mbarszcz-pcb/c64-rf-modulator-replacement/images/c64-rf-modulator-render-top.PNG

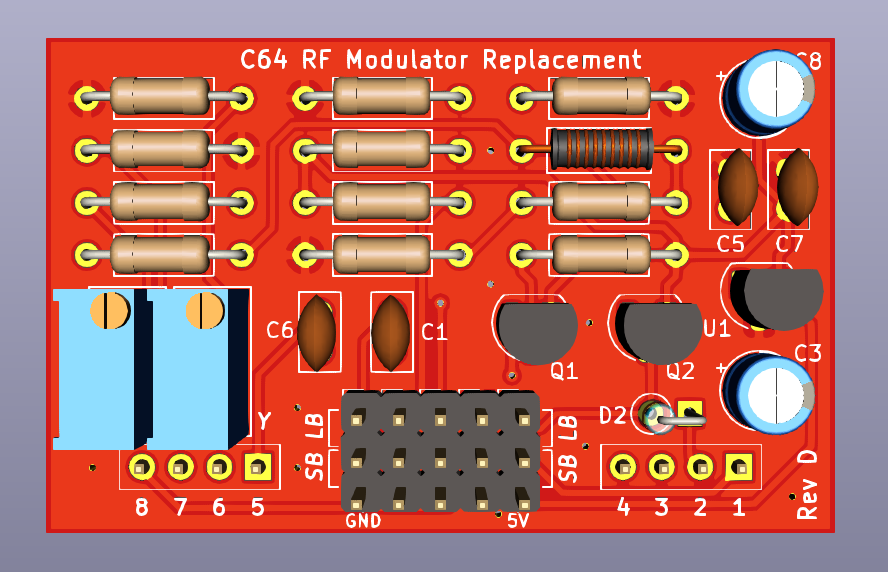
images/c64-rf-modulator-render-top.PNG
