mbarszcz-pcb/c64-rf-modulator-replacement/images/pcb/c64-rf-modulator-pcb-top.PNG

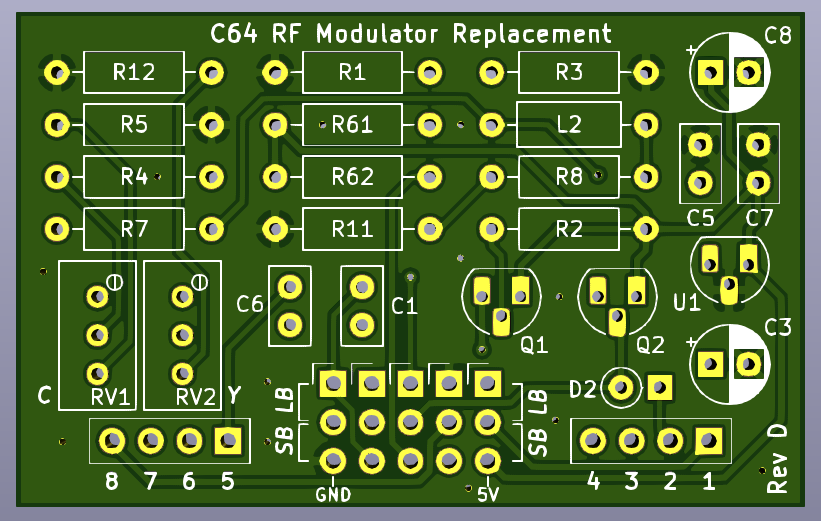
images/pcb/c64-rf-modulator-pcb-top.PNG
