mbarszcz-pcb/c64-rf-modulator-replacement/images/photos/c64-rf-modulator-photo-inst.png

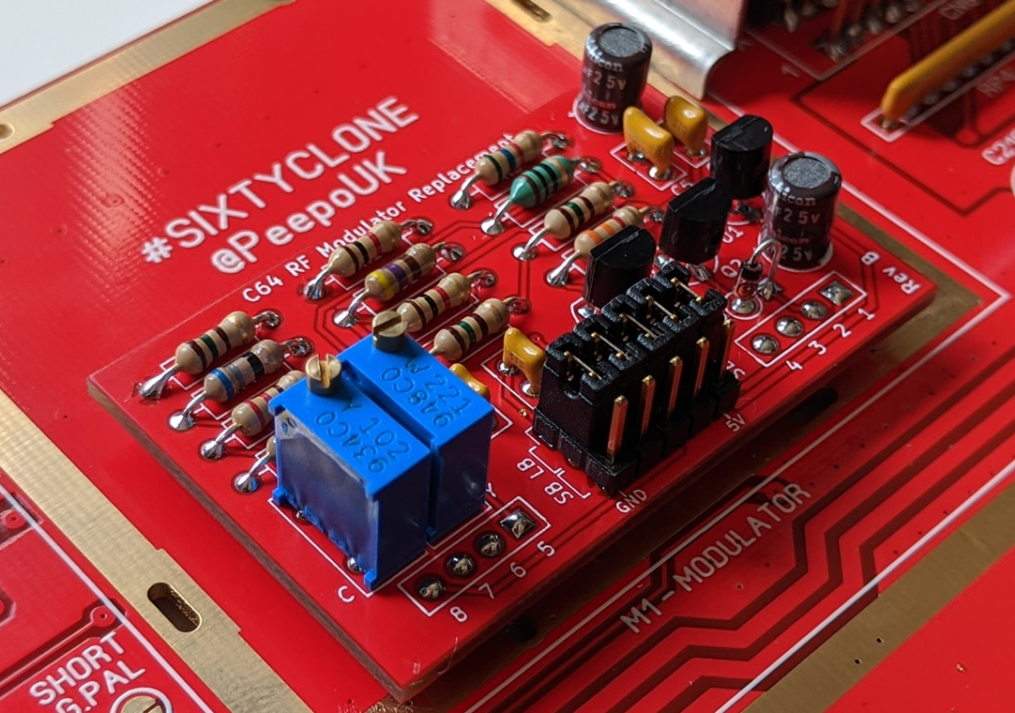
images/photos/c64-rf-modulator-photo-inst.png
